robinhedwards/UnoCart/source/Atari/UnoCartROM/rom.h

unsigned char UnoCart_rom[] = {
  0x60, 0xa9, 0x8f, 0x8d, 0xc5, 0x02, 0xa9, 0x82, 0x8d, 0xc6, 0x02, 0xa9,
  0x03, 0x85, 0x09, 0xa9, 0x7d, 0x85, 0x02, 0xa9, 0xa2, 0x85, 0x03, 0x20,
  0x53, 0xa4, 0x20, 0x21, 0xa6, 0x20, 0x38, 0xa6, 0x20, 0x90, 0xa3, 0xa9,
  0x00, 0x85, 0x87, 0xa9, 0x01, 0x20, 0x20, 0x06, 0xad, 0x01, 0xd5, 0xc9,
  0x01, 0xd0, 0x06, 0x20, 0x87, 0xa2, 0x4c, 0x23, 0xa0, 0xad, 0x02, 0xd5,
  0x85, 0x80, 0xa9, 0x00, 0x85, 0x84, 0xa9, 0x00, 0x85, 0x85, 0x20, 0xc2,
  0xa4, 0x20, 0x3b, 0xa3, 0xa5, 0x80, 0xd0, 0x09, 0x20, 0xed, 0xa4, 0x20,
  0x09, 0xa4, 0x4c, 0x5f, 0xa0, 0x20, 0xde, 0xa2, 0x20, 0x70, 0xa3, 0x20,
  0x7e, 0xa3, 0xf0, 0xfb, 0xc9, 0x1c, 0xf0, 0x57, 0xc9, 0x2d, 0xf0, 0x53,
  0xc9, 0x1d, 0xf0, 0x2a, 0xc9, 0x3d, 0xf0, 0x26, 0xc9, 0x62, 0xd0, 0x03,
  0x4c, 0x13, 0xa1, 0xc9, 0x1e, 0xd0, 0x03, 0x4c, 0x13, 0xa1, 0xc9, 0x9b,
  0xd0, 0x03, 0x4c, 0xdd, 0xa0, 0xc9, 0x78, 0xd0, 0x03, 0x4c, 0x21, 0xa1,
  0xc9, 0x1b, 0xd0, 0x03, 0x4c, 0x42, 0xa1, 0x4c, 0x5f, 0xa0, 0xa5, 0x85,
  0x18, 0x69, 0x01, 0xc5, 0x80, 0xb0, 0xbc, 0xe6, 0x85, 0xa5, 0x85, 0x38,
  0xe5, 0x84, 0x18, 0xc9, 0x0f, 0xf0, 0x06, 0x20, 0x70, 0xa3, 0x4c, 0x5f,
  0xa0, 0xa5, 0x84, 0x18, 0x69, 0x0f, 0x85, 0x84, 0x4c, 0x46, 0xa0, 0xa5,
  0x85, 0xc9, 0x00, 0xf0, 0x9a, 0xc6, 0x85, 0xa5, 0x85, 0xc5, 0x84, 0x30,
  0x06, 0x20, 0x70, 0xa3, 0x4c, 0x5f, 0xa0, 0xa5, 0x84, 0x38, 0xe9, 0x0f,
  0x85, 0x84, 0x4c, 0x46, 0xa0, 0xa5, 0x80, 0xd0, 0x03, 0x4c, 0x5f, 0xa0,
  0xa5, 0x85, 0x8d, 0x00, 0xd5, 0xa9, 0x00, 0x20, 0x20, 0x06, 0xad, 0x01,
  0xd5, 0xc9, 0x00, 0xf0, 0x12, 0xc9, 0x01, 0xf0, 0x11, 0xc9, 0x02, 0xf0,
  0x10, 0xc9, 0x03, 0xf0, 0x0f, 0x20, 0x87, 0xa2, 0x4c, 0x23, 0xa0, 0x4c,
  0x23, 0xa0, 0x4c, 0x30, 0x06, 0x4c, 0x29, 0xa1, 0x4c, 0x32, 0xa1, 0xa5,
  0x87, 0xc9, 0x01, 0xf0, 0x05, 0xa9, 0x03, 0x20, 0x20, 0x06, 0x4c, 0x23,
  0xa0, 0xa9, 0xfe, 0x20, 0x20, 0x06, 0x4c, 0x30, 0x06, 0x20, 0xdc, 0xa3,
  0x20, 0x4d, 0xa6, 0x4c, 0x03, 0x07, 0x20, 0xdc, 0xa3, 0x20, 0x76, 0xa1,
  0xc9, 0x00, 0xf0, 0x03, 0x4c, 0x23, 0xa0, 0x4c, 0x30, 0x06, 0x20, 0x1d,
  0xa5, 0x20, 0x03, 0xa2, 0xa5, 0x86, 0xc9, 0x00, 0xd0, 0x03, 0x4c, 0x46,
  0xa0, 0xa0, 0x00, 0xb9, 0x00, 0x06, 0x99, 0x00, 0xd5, 0xc8, 0x98, 0xc5,
  0x86, 0x90, 0xf4, 0xa9, 0x00, 0x99, 0x00, 0xd5, 0x20, 0x3b, 0xa3, 0x20,
  0x05, 0xa5, 0xa9, 0x05, 0x20, 0x20, 0x06, 0xa9, 0x01, 0x85, 0x87, 0x4c,
  0x2c, 0xa0, 0xa9, 0x10, 0x20, 0x20, 0x06, 0xad, 0x01, 0xd5, 0xc9, 0x01,
  0xd0, 0x06, 0x20, 0x87, 0xa2, 0xa9, 0x01, 0x60, 0x08, 0x78, 0xad, 0x0e,
  0xd4, 0x48, 0xa9, 0x00, 0x8d, 0x0e, 0xd4, 0xa9, 0xb2, 0x8d, 0x17, 0xd0,
  0xa9, 0xb2, 0x8d, 0x18, 0xd0, 0xad, 0x01, 0xd3, 0x29, 0xfe, 0x8d, 0x01,
  0xd3, 0xa9, 0x00, 0x85, 0x90, 0xa9, 0xc0, 0x85, 0x91, 0xa9, 0x00, 0x85,
  0x99, 0xa5, 0x91, 0xc9, 0xd0, 0xd0, 0x08, 0xa9, 0xd8, 0x85, 0x91, 0xa9,
  0x30, 0x85, 0x99, 0xa9, 0x00, 0x85, 0x90, 0xa5, 0x99, 0x8d, 0x00, 0xd5,
  0xa9, 0x11, 0x20, 0x20, 0x06, 0xa0, 0x00, 0xb9, 0x01, 0xd5, 0x91, 0x90,
  0xc8, 0xc0, 0x80, 0xd0, 0xf6, 0xe6, 0x99, 0xa9, 0x80, 0x85, 0x90, 0xa5,
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
};
unsigned int UnoCart_rom_len = 8192;
